LineF/HM-Sensor/cppfix.cpp

/*
 * cppfix.h
 *
 * Created: 12.09.2016 22:29:18
 *  Author: Martin
 */ 


#ifndef CPPFIX_H_
#define CPPFIX_H_

#include <stdlib.h>
/*
__extension__ typedef int __guard __attribute__((mode (__DI__)));

void * operator new(size_t size);
void operator delete(void * ptr);

int __cxa_guard_acquire(__guard *g) {return !*(char *)(g);};
void __cxa_guard_release (__guard *g) {*(char *)g = 1;};
void __cxa_guard_abort (__guard *) {};
*/

void * operator new(size_t size)
{
	return malloc(size);
}

void * operator new [](size_t size)
{
	return malloc(size);
}

void operator delete(void * ptr)
{
	free(ptr);
}

#endif /* CPPFIX_H_ */
